Jankyneering/rack-ui/firmware/src/User/animations.c

/**
 ******************************************************************************
 * @file    animations.c
 * @brief   LED animation engine for the Charlieplex LEDs.
 *
 * The active animation is selected through register 0x0E (REG_ANIMATION):
 *   0x00 = IDLE     : custom control over the LEDs via registers 0x10-0x1B
 *   0x01 = LOADING  : rotating loading animation
 *   0x02 = FLASHING : all LEDs flash on and off
 * Register 0x0F (REG_ANIMATION_SETTINGS) holds the setting of the
 *   selected animation (timing, brightness or gauge maximum); writing
 *   REG_ANIMATION loads that animation's default.
 ******************************************************************************
 */

#include "animations.h"
#include "main.h"
#include <stdlib.h>

/* External variables from main.c */
extern volatile uint32_t sys_tick_ms;
extern volatile uint8_t device_memory[REG_COUNT];

typedef void (*Animation_Start_Fn_t)(void);
typedef void (*Animation_Step_Fn_t)(void);

/* One entry per animation exposed through register 0x0E. To add a new
 * animation: give it an ID in Animation_Id_t, implement its start/step
 * functions and append an entry here. */
typedef struct {
    uint8_t id;
    Animation_Start_Fn_t start;
    Animation_Step_Fn_t step;
} Animation_Entry_t;

/* Timing setting (register 0x0F) of the active animation and its scale, in ms
 * per register step. A scale of 0 means the register is ignored. */
static uint8_t animation_settings    = 0;
static uint8_t animation_settings_ms = 0;

static const Animation_Entry_t *Animation_Find(uint8_t id);
static void Animation_Idle_Start(void);
static void Animation_Idle_Step(void);
static void Animation_Loading_Start(void);
static void Animation_Loading_Step(void);
static void Animation_Flashing_Start(void);
static void Animation_Flashing_Step(void);
static void Animation_Pulsing_Start(void);
static void Animation_Pulsing_Step(void);
static void Animation_Breathing_Start(void);
static void Animation_Breathing_Step(void);

static void Animation_Following_Start(void);
static void Animation_Following_Step(void);
static void Animation_Point_Start(void);
static void Animation_Point_Step(void);
static void Animation_Gauge_Start(void);
static void Animation_Gauge_Step(void);
static void Animation_Gauge_Center_Start(void);
static void Animation_Gauge_Center_Step(void);

static void Animation_All_On_Start(void);
static void Animation_All_On_Step(void);
static void Animation_All_Off_Start(void);
static void Animation_All_Off_Step(void);

static const Animation_Entry_t animation_table[] = {
    {ANIMATION_IDLE, Animation_Idle_Start, Animation_Idle_Step},
    {ANIMATION_LOADING, Animation_Loading_Start, Animation_Loading_Step},
    {ANIMATION_FLASHING, Animation_Flashing_Start, Animation_Flashing_Step},
    {ANIMATION_PULSING, Animation_Pulsing_Start, Animation_Pulsing_Step},
    {ANIMATION_BREATHING, Animation_Breathing_Start, Animation_Breathing_Step},

    {ANIMATION_FOLLOWING, Animation_Following_Start, Animation_Following_Step},
    {ANIMATION_POINT, Animation_Point_Start, Animation_Point_Step},
    {ANIMATION_GAUGE, Animation_Gauge_Start, Animation_Gauge_Step},
    {ANIMATION_GAUGE_CENTER, Animation_Gauge_Center_Start, Animation_Gauge_Center_Step},

    {ANIMATION_ALL_ON, Animation_All_On_Start, Animation_All_On_Step},
    {ANIMATION_ALL_OFF, Animation_All_Off_Start, Animation_All_Off_Step},
};

static const Animation_Entry_t *active_animation = &animation_table[0];
static uint8_t current_id                        = ANIMATION_IDLE;

/* Default timing setting (register 0x0F) for a given animation id: the value
 * written to REG_ANIMATION_SETTINGS when the animation is selected. */
static uint8_t Animation_SettingsDefault(uint8_t id) {
    switch (id) {
    case ANIMATION_LOADING:
        return ANIMATION_LOADING_SETTINGS_DEFAULT;
    case ANIMATION_FLASHING:
        return ANIMATION_FLASHING_SETTINGS_DEFAULT;
    case ANIMATION_PULSING:
        return ANIMATION_PULSING_SETTINGS_DEFAULT;
    case ANIMATION_ALL_ON:
        return ANIMATION_ALL_ON_SETTINGS_DEFAULT;
    case ANIMATION_FOLLOWING:
        return ANIMATION_FOLLOWING_SETTINGS_DEFAULT;
    case ANIMATION_POINT:
        return ANIMATION_POINT_SETTINGS_DEFAULT;
    case ANIMATION_GAUGE:
        return ANIMATION_GAUGE_SETTINGS_DEFAULT;
    case ANIMATION_GAUGE_CENTER:
        return ANIMATION_GAUGE_CENTER_SETTINGS_DEFAULT;
    default:
        return 0;
    }
}

static uint8_t Animation_SettingsMs(uint8_t id) {
    switch (id) {
    case ANIMATION_LOADING:
        return ANIMATION_LOADING_SETTINGS_MS;
    case ANIMATION_FLASHING:
        return ANIMATION_FLASHING_SETTINGS_MS;
    case ANIMATION_PULSING:
        return ANIMATION_PULSING_SETTINGS_MS;
    default:
        return 0;
    }
}

static uint32_t Animation_SettingsTickMs(void) {
    return (uint32_t)animation_settings * animation_settings_ms;
}

void Animations_Init(void) {
    current_id                            = ANIMATION_DEFAULT;
    active_animation                      = Animation_Find(ANIMATION_DEFAULT);
    animation_settings                    = Animation_SettingsDefault(current_id);
    animation_settings_ms                 = Animation_SettingsMs(current_id);
    device_memory[REG_ANIMATION_SETTINGS] = animation_settings;
    active_animation->start();
}

void Animations_Set(uint8_t id) {
    const Animation_Entry_t *entry = Animation_Find(id);
    current_id                     = id;
    if (entry == NULL)
        entry = Animation_Find(ANIMATION_IDLE); // unknown value: fall back to IDLE
    if (entry != active_animation) {
        active_animation = entry;
        entry->start();
    }
    animation_settings                    = Animation_SettingsDefault(id);
    animation_settings_ms                 = Animation_SettingsMs(id);
    device_memory[REG_ANIMATION_SETTINGS] = animation_settings;
}

void Animations_SetSettings(uint8_t settings) {
    if (settings == 0) {
        // 0 keeps the current setting; undo the ISR's register write
        device_memory[REG_ANIMATION_SETTINGS] = animation_settings;
        return;
    }
    animation_settings                    = settings;
    device_memory[REG_ANIMATION_SETTINGS] = animation_settings;
    if (current_id == ANIMATION_ALL_ON) {
        for (uint8_t i = 0; i < ANIMATION_LED_COUNT; i++) {
            device_memory[REG_LED_BASE + i] = animation_settings;
        }
        APP_MarkRegsDirty();
    }
}

uint8_t Animations_GetSettings(void) {
    return animation_settings;
}

uint8_t Animations_Get(void) {
    return current_id;
}

void Animations_Tick(void) {
    static uint32_t last_tick = 0;

    if ((sys_tick_ms - last_tick) < ANIMATION_TICK_MS)
        return;
    last_tick = sys_tick_ms;

    active_animation->step();
}

static const Animation_Entry_t *Animation_Find(uint8_t id) {
    for (uint8_t i = 0; i < (sizeof(animation_table) / sizeof(animation_table[0])); i++) {
        if (animation_table[i].id == id)
            return &animation_table[i];
    }
    return NULL;
}

/**
 * @brief IDLE: the LEDs are driven manually through registers 0x10-0x1B.
 */
static void Animation_Idle_Start(void) {
    /* Nothing to reset: the master owns the LED brightness registers. */
}

static void Animation_Idle_Step(void) {
    /* Nothing to do: LED register writes are applied by the main loop. */
}

/* Standalone animations */

/**
 * @brief Perform a rotating loading animation on the Charlieplex LEDs.
 * This animation lights up each LED in a circular pattern, with each LED
 * reaching maximum brightness before moving to the next.
 */
static uint8_t loading_brightness_lut[ANIMATION_LED_COUNT];
static uint8_t loading_current_led = 0;
static uint32_t last_loading_tick  = 0;

static void Animation_Loading_Start(void) {
    // Build a simple linear LUT for the loading animation brightnesses
    for (uint8_t i = 1; i < ANIMATION_LED_COUNT; i++) {
        // Calculate the brightness for each LED in the loading animation
        loading_brightness_lut[i] =
            (uint8_t)(((uint16_t)(i + 1) * CHARLIE_PWM_STEPS) / ANIMATION_LED_COUNT - 1);
    }
    loading_current_led = 0;
    last_loading_tick   = sys_tick_ms;
}

static void Animation_Loading_Step(void) {
    uint32_t tick_ms = Animation_SettingsTickMs();
    if (tick_ms > 0 && (sys_tick_ms - last_loading_tick) >= tick_ms) {
        last_loading_tick   = sys_tick_ms;

        loading_current_led = (loading_current_led + 1) % ANIMATION_LED_COUNT;

        // Apply the calculated brightnesses to all LEDs
        for (uint8_t i = 0; i < ANIMATION_LED_COUNT; i++) {
            uint8_t led_index                       = (loading_current_led + i) % ANIMATION_LED_COUNT;
            device_memory[REG_LED_BASE + led_index] = loading_brightness_lut[i];
        }

        // Mark the registers as dirty so that the main loop applies the changes
        APP_MarkRegsDirty();
    }
}

/**
 * @brief Perform a flashing animation on the Charlieplex LEDs.
 * This animation makes all LEDs flash on and off in a synchronized manner.
 */
static uint32_t last_flashing_tick = 0;
static bool flashing_state         = false;

static void Animation_Flashing_Start(void) {
    flashing_state     = 0;
    last_flashing_tick = sys_tick_ms;
}

static void Animation_Flashing_Step(void) {
    uint32_t tick_ms = Animation_SettingsTickMs();
    if (tick_ms > 0 && (sys_tick_ms - last_flashing_tick) >= tick_ms) {
        last_flashing_tick = sys_tick_ms;

        flashing_state     = !flashing_state;

        // Apply the flashing state to all LEDs
        for (uint8_t i = 0; i < ANIMATION_LED_COUNT; i++) {
            device_memory[REG_LED_BASE + i] = flashing_state ? CHARLIE_PWM_STEPS - 1 : 0;
        }

        // Mark the registers as dirty so that the main loop applies the changes
        APP_MarkRegsDirty();
    }
}

/**
 * @brief Perform a pulsing animation on the Charlieplex LEDs.
 * This animation smoothly increases and decreases the brightness of all LEDs.
 */
static uint32_t last_pulsing_tick = 0;
static uint8_t pulsing_brightness = 0;
static int8_t pulsing_direction   = 1;

static void Animation_Pulsing_Start(void) {
    pulsing_brightness = 0;
    pulsing_direction  = 1;
    last_pulsing_tick  = sys_tick_ms;
}

static void Animation_Pulsing_Step(void) {
    uint32_t tick_ms = Animation_SettingsTickMs();
    if (tick_ms > 0 && (sys_tick_ms - last_pulsing_tick) >= tick_ms) {
        last_pulsing_tick = sys_tick_ms;

        // Update the brightness
        pulsing_brightness += pulsing_direction;

        // Change direction if we reach the limits
        if (pulsing_brightness >= CHARLIE_PWM_STEPS - 1) {
            pulsing_brightness = CHARLIE_PWM_STEPS - 1;
            pulsing_direction  = -1;
        } else if (pulsing_brightness <= 0) {
            pulsing_brightness = 0;
            pulsing_direction  = 1;
        }

        // Apply the current brightness to all LEDs
        for (uint8_t i = 0; i < ANIMATION_LED_COUNT; i++) {
            device_memory[REG_LED_BASE + i] = pulsing_brightness;
        }

        // Mark the registers as dirty so that the main loop applies the changes
        APP_MarkRegsDirty();
    }
}

/**
 * @brief Perform a breathing animation on the Charlieplex LEDs.
 * This animation smoothly increases and decreases the brightness of all LEDs.
 */
typedef enum {
    ANIMATION_BREATHING_PHASE_IN,
    ANIMATION_BREATHING_PHASE_HOLD,
    ANIMATION_BREATHING_PHASE_OUT,
    ANIMATION_BREATHING_PHASE_PAUSE,
} BreathingPhase_t;

static BreathingPhase_t breathing_phase    = ANIMATION_BREATHING_PHASE_IN;
static uint32_t breathing_phase_start_tick = 0;

static void Animation_Breathing_Start(void) {
    breathing_phase            = ANIMATION_BREATHING_PHASE_IN;
    breathing_phase_start_tick = sys_tick_ms;
}

static void Animation_Breathing_Step(void) {
    uint32_t elapsed = sys_tick_ms - breathing_phase_start_tick;

    switch (breathing_phase) {
    case ANIMATION_BREATHING_PHASE_IN:
        if (elapsed >= ANIMATION_BREATHING_IN_MS) {
            breathing_phase            = ANIMATION_BREATHING_PHASE_HOLD;
            breathing_phase_start_tick = sys_tick_ms;
            elapsed                    = 0;
        }
        break;
    case ANIMATION_BREATHING_PHASE_HOLD:
        if (elapsed >= ANIMATION_BREATHING_HOLD_MS) {
            breathing_phase            = ANIMATION_BREATHING_PHASE_OUT;
            breathing_phase_start_tick = sys_tick_ms;
            elapsed                    = 0;
        }
        break;
    case ANIMATION_BREATHING_PHASE_OUT:
        if (elapsed >= ANIMATION_BREATHING_OUT_MS) {
            breathing_phase            = ANIMATION_BREATHING_PHASE_PAUSE;
            breathing_phase_start_tick = sys_tick_ms;
            elapsed                    = 0;
        }
        break;
    case ANIMATION_BREATHING_PHASE_PAUSE:
        if (elapsed >= ANIMATION_BREATHING_PAUSE_MS) {
            breathing_phase            = ANIMATION_BREATHING_PHASE_IN;
            breathing_phase_start_tick = sys_tick_ms;
            elapsed                    = 0;
        }
        break;
    default:
        // Unknown phase, reset to IN
        breathing_phase            = ANIMATION_BREATHING_PHASE_IN;
        breathing_phase_start_tick = sys_tick_ms;
        elapsed                    = 0;
        break;
    }

    // Calculate brightness based on the current phase and elapsed time
    uint8_t brightness = 0;

    switch (breathing_phase) {
    case ANIMATION_BREATHING_PHASE_IN:
        brightness = (uint8_t)((elapsed * CHARLIE_PWM_STEPS) / ANIMATION_BREATHING_IN_MS);
        break;
    case ANIMATION_BREATHING_PHASE_HOLD:
        brightness = CHARLIE_PWM_STEPS; // Full brightness
        break;
    case ANIMATION_BREATHING_PHASE_OUT:
        brightness =
            (uint8_t)(CHARLIE_PWM_STEPS -
                      ((elapsed * CHARLIE_PWM_STEPS) / ANIMATION_BREATHING_OUT_MS));
        break;
    case ANIMATION_BREATHING_PHASE_PAUSE:
        brightness = 0; // Off
        break;
    default:
        brightness = 0; // Default to off
        break;
    }

    // Apply the calculated brightness to all LEDs
    for (uint8_t i = 0; i < ANIMATION_LED_COUNT; i++) {
        device_memory[REG_LED_BASE + i] = brightness;
    }

    // Mark the registers as dirty so that the main loop applies the changes
    APP_MarkRegsDirty();
}

/* Animations with encoder reactions */

/**
 * @brief Perform a following animation on the Charlieplex LEDs.
 * This animation lights up one in three LEDs based on the encoder rotation, creating a "following" effect.
 */
static void Animation_Following_Start(void) {
    // Nothing to reset: the master owns the LED brightness registers.
}

static void Animation_Following_Step(void) {
    // Get the current encoder rotation count
    int16_t rotation_count = (device_memory[REG_ENC_COUNT_LO] | (device_memory[REG_ENC_COUNT_HI] << 8));
    // Set LED states; the animation setting (register 0x0F) is the brightness
    // of the LEDs that are not lit
    for (uint8_t i = 0; i < ANIMATION_LED_COUNT; i++) {
        device_memory[REG_LED_BASE + i] = (i - rotation_count) % ANIMATION_FOLLOWING_LED_STEPS == 0 ? CHARLIE_PWM_STEPS - 1 : animation_settings; // Light up every third LED
    }
    // Mark the registers as dirty so that the main loop applies the changes
    APP_MarkRegsDirty();
}

/**
 * @brief Perform a point animation on the Charlieplex LEDs.
 * This animation lights up one LED at a time based on the encoder rotation, creating a "pointing" effect.
 */
static void Animation_Point_Start(void) {
    // Nothing to reset: the master owns the LED brightness registers.
}

static void Animation_Point_Step(void) {
    // Get the current encoder rotation count
    int16_t rotation_count = (device_memory[REG_ENC_COUNT_LO] | (device_memory[REG_ENC_COUNT_HI] << 8));
    // Set LED states; the animation setting (register 0x0F) is the brightness
    // of the LEDs that are not lit
    for (uint8_t i = 0; i < ANIMATION_LED_COUNT; i++) {
        device_memory[REG_LED_BASE + i] = (i - rotation_count) % CHARLIE_LED_COUNT == 0 ? CHARLIE_PWM_STEPS - 1 : animation_settings;
    }
    // Mark the registers as dirty so that the main loop applies the changes
    APP_MarkRegsDirty();
}

/**
 * @brief Perform a gauge animation on the Charlieplex LEDs.
 * This animation lights up LEDs in a gauge pattern based on the encoder rotation.
 */
static uint32_t last_gauge_tick = 0;
static void Animation_Gauge_Start(void) {
    // Reset encoder count to zero for a fresh start (signed 16-bit value)
    device_memory[REG_ENC_COUNT_HI] = 0x00;
    device_memory[REG_ENC_COUNT_LO] = 0x00;

    last_gauge_tick                 = sys_tick_ms;
}

static void Animation_Gauge_Step(void) {
    if ((sys_tick_ms - last_gauge_tick) < 50) // Update every 50ms
        return;
    last_gauge_tick = sys_tick_ms;

    // The animation setting (register 0x0F) is the maximum gauge value the
    // encoder count is scaled against (e.g. 10, 100, 250)
    int16_t gauge_max = animation_settings;

    // Get the current encoder rotation count
    int16_t rotation_count = (device_memory[REG_ENC_COUNT_LO] | (device_memory[REG_ENC_COUNT_HI] << 8));

    // Clamp the count to the 0-gauge_max range
    if (rotation_count < 0) {
        rotation_count = 0;
        // clamp device_memory[REG_ENC_COUNT_HI] and device_memory[REG_ENC_COUNT_LO] to 0
        device_memory[REG_ENC_COUNT_HI] = (uint8_t)((rotation_count >> 8) & 0xFF);
        device_memory[REG_ENC_COUNT_LO] = (uint8_t)(rotation_count & 0xFF);
    } else if (rotation_count > gauge_max) {
        rotation_count = gauge_max;
        // clamp device_memory[REG_ENC_COUNT_HI] and device_memory[REG_ENC_COUNT_LO] to gauge_max
        device_memory[REG_ENC_COUNT_HI] = (uint8_t)((rotation_count >> 8) & 0xFF);
        device_memory[REG_ENC_COUNT_LO] = (uint8_t)(rotation_count & 0xFF);
    }

#ifdef ANIMATION_GAUGE_DIM_UNUSED_LEDS
    // Hold the LEDs that are not part of the gauge arc at a low brightness
    // instead of keeping the state the previous animation left them in
    for (uint8_t i = ANIMATION_GAUGE_LED_COUNT; i < CHARLIE_LED_COUNT; i++) {
        device_memory[REG_LED_BASE + (i + ANIMATION_GAUGE_START_LED) % CHARLIE_LED_COUNT] =
            ANIMATION_GAUGE_UNUSED_BRIGHTNESS;
    }
#endif

    // calculate the brightness for each LED based on the scaled gauge value
    // the gauge is divided evenly across the arc LEDs, e.g. with a max of 100
    // and 9 LEDs, each LED covers an 11.1-unit range of the gauge
    for (uint8_t i = 0; i < ANIMATION_GAUGE_LED_COUNT; i++) {
        // calculate the value range for this LED
        float led_percentage_start = ((float)i * gauge_max) / ANIMATION_GAUGE_LED_COUNT;
        float led_percentage_end   = ((float)(i + 1) * gauge_max) / ANIMATION_GAUGE_LED_COUNT;

        if (rotation_count >= led_percentage_end) {
            // LED is fully lit
            device_memory[REG_LED_BASE + (i + ANIMATION_GAUGE_START_LED) % CHARLIE_LED_COUNT] = CHARLIE_PWM_STEPS - 1;
        } else if (rotation_count <= led_percentage_start) {
            // LED is off
            device_memory[REG_LED_BASE + (i + ANIMATION_GAUGE_START_LED) % CHARLIE_LED_COUNT] = 0;
        } else {
            // LED is partially lit, calculate brightness based on the scaled value
            float led_range                                                                   = led_percentage_end - led_percentage_start;
            float led_brightness_percentage                                                   = (rotation_count - led_percentage_start) / led_range;
            device_memory[REG_LED_BASE + (i + ANIMATION_GAUGE_START_LED) % CHARLIE_LED_COUNT] = (uint8_t)(led_brightness_percentage * (CHARLIE_PWM_STEPS - 1));
        }
    }

    // Mark the registers as dirty so that the main loop applies the changes
    APP_MarkRegsDirty();
}

/**
 * @brief Perform a centered gauge animation on the Charlieplex LEDs.
 * This animation lights up LEDs outward from the center LED based on the
 * encoder rotation: positive counts fill one direction, negative counts the
 * other, up to the positive/negative limit set through register 0x0F.
 */
static uint32_t last_gauge_center_tick = 0;
static void Animation_Gauge_Center_Start(void) {
    // Reset encoder count to zero for a fresh start (signed 16-bit value)
    device_memory[REG_ENC_COUNT_HI] = 0x00;
    device_memory[REG_ENC_COUNT_LO] = 0x00;

    last_gauge_center_tick          = sys_tick_ms;
}

static void Animation_Gauge_Center_Step(void) {
    if ((sys_tick_ms - last_gauge_center_tick) < 50) // Update every 50ms
        return;
    last_gauge_center_tick = sys_tick_ms;

    // The animation setting (register 0x0F) is the positive/negative gauge
    // limit the encoder count is scaled against (e.g. 10, 100, 250); the count
    // is clamped symmetrically to -gauge_center_max..+gauge_center_max
    int16_t gauge_center_max = animation_settings;

    // Get the current encoder rotation count
    int16_t rotation_count = (device_memory[REG_ENC_COUNT_LO] | (device_memory[REG_ENC_COUNT_HI] << 8));

    // Clamp the count to the -gauge_center_max..+gauge_center_max range
    if (rotation_count < -(gauge_center_max)) {
        rotation_count = -(gauge_center_max);
        // clamp device_memory[REG_ENC_COUNT_HI] and device_memory[REG_ENC_COUNT_LO] to -(gauge_center_max)
        device_memory[REG_ENC_COUNT_HI] = (uint8_t)((rotation_count >> 8) & 0xFF);
        device_memory[REG_ENC_COUNT_LO] = (uint8_t)(rotation_count & 0xFF);
    } else if (rotation_count > gauge_center_max) {
        rotation_count = gauge_center_max;
        // clamp device_memory[REG_ENC_COUNT_HI] and device_memory[REG_ENC_COUNT_LO] to gauge_max
        device_memory[REG_ENC_COUNT_HI] = (uint8_t)((rotation_count >> 8) & 0xFF);
        device_memory[REG_ENC_COUNT_LO] = (uint8_t)(rotation_count & 0xFF);
    }

#ifdef ANIMATION_GAUGE_DIM_UNUSED_LEDS
    // Hold the LEDs that are not part of the gauge arc at a low brightness
    // instead of keeping the state the previous animation left them in
    for (uint8_t i = ANIMATION_GAUGE_LED_COUNT; i < CHARLIE_LED_COUNT; i++) {
        device_memory[REG_LED_BASE + (i + ANIMATION_GAUGE_START_LED) % CHARLIE_LED_COUNT] =
            ANIMATION_GAUGE_UNUSED_BRIGHTNESS;
    }
#endif

    // calculate the brightness for each LED based on the scaled gauge value
    // the gauge is divided evenly across the arc LEDs going up or down from the
    // center LED, e.g. with a min/max of 50 and 4 LEDs per side, each LED covers
    // a 12.5-unit range of the gauge. The center LED is always lit at full
    // brightness, the LEDs to the left and right of it are lit based on the
    // encoder count, up to the 4th LED on either side of the center LED.
    int value                 = abs((int)rotation_count);
    bool is_negative          = rotation_count < 0;
    uint8_t side_led_count    = (ANIMATION_GAUGE_LED_COUNT - 1) / 2;
    uint8_t center_led        = (ANIMATION_GAUGE_START_LED + side_led_count) % CHARLIE_LED_COUNT;

    // Center LED is always lit at full brightness
    device_memory[REG_LED_BASE + center_led] = CHARLIE_PWM_STEPS - 1;

    for (uint8_t i = 0; i < side_led_count; i++) {
        // calculate the value range for this LED
        float led_percentage_start = ((float)i * gauge_center_max) / side_led_count;
        float led_percentage_end   = ((float)(i + 1) * gauge_center_max) / side_led_count;

        uint8_t level = 0;
        if (value >= led_percentage_end) {
            // LED is fully lit
            level = CHARLIE_PWM_STEPS - 1;
        } else if (value <= led_percentage_start) {
            // LED is off
            level = 0;
        } else {
            // LED is partially lit, calculate brightness based on the scaled value
            float led_range                  = led_percentage_end - led_percentage_start;
            float led_brightness_percentage  = (value - led_percentage_start) / led_range;
            level                            = (uint8_t)(led_brightness_percentage * (CHARLIE_PWM_STEPS - 1));
        }

        // write both sides every step so the inactive side is turned off
        // instead of keeping the level it had before the count flipped sign
        int8_t offset = (int8_t)(i + 1);
        uint8_t positive_led = (uint8_t)(center_led + CHARLIE_LED_COUNT + offset) % CHARLIE_LED_COUNT;
        uint8_t negative_led = (uint8_t)(center_led + CHARLIE_LED_COUNT - offset) % CHARLIE_LED_COUNT;
        device_memory[REG_LED_BASE + positive_led] = is_negative ? 0 : level;
        device_memory[REG_LED_BASE + negative_led] = is_negative ? level : 0;
    }

    // Mark the registers as dirty so that the main loop applies the changes
    APP_MarkRegsDirty();
}

/**
 * @brief Turn all LEDs on at set brightness.
 * The brightness is the animation setting (register 0x0F).
 */
static void Animation_All_On_Start(void) {
    // No startup action needed; the step function will set the brightness.
}
static void Animation_All_On_Step(void) {
    for (uint8_t i = 0; i < ANIMATION_LED_COUNT; i++) {
        device_memory[REG_LED_BASE + i] = animation_settings;
    }

    // Mark the registers as dirty so that the main loop applies the changes
    APP_MarkRegsDirty();
}

/**
 * @brief Turn all LEDs off.
 */
static void Animation_All_Off_Start(void) {
    // No startup action needed; the step function will turn off the LEDs.
}
static void Animation_All_Off_Step(void) {
    for (uint8_t i = 0; i < ANIMATION_LED_COUNT; i++) {
        device_memory[REG_LED_BASE + i] = 0;
    }
    APP_MarkRegsDirty();
}
