Jankyneering/rack-ui/software/scripts/ssd1306.py

"""Minimal SSD1306 128x64 OLED driver for the host-side test scripts.

Drives the display directly through an i2cdriver.I2CDriver instance on the
same bus as the rack-ui MCU, so no firmware changes are needed. No external
dependencies: a classic 5x7 bitmap font is embedded.

Coordinate system: (0,0) is the top-left corner, x grows to the right, y grows
down. The framebuffer is page-major: one byte per column covers 8 vertical
pixels, LSB = topmost row of the page. On the common two-color modules the
top 16 rows (y 0-15) are yellow and the rest is blue, which makes rows 0-15 a
natural title band.

The SSD1306 GDDRAM is undefined at power-up, so init() pushes a full clear to
the display. Only dirty pages are re-sent afterwards; the shadow copy of the
last flushed content makes that bookkeeping possible.
"""

WIDTH = 128
HEIGHT = 64
PAGE_COUNT = HEIGHT // 8

I2C_ADDRESSES = (0x3C, 0x3D)

# Control bytes: Co=0 (following bytes all share this D/C state)
CMD = 0x00
DATA = 0x40

# Classic 5x7 bitmap font, ASCII 0x20-0x7E, 5 bytes per glyph, LSB = top row.
FONT5X7 = (
    0x00, 0x00, 0x00, 0x00, 0x00, 0x00, 0x00, 0x5F, 0x00, 0x00, 0x00, 0x07,
    0x00, 0x07, 0x00, 0x14, 0x7F, 0x14, 0x7F, 0x14, 0x24, 0x2A, 0x7F, 0x2A,
    0x12, 0x23, 0x13, 0x08, 0x64, 0x62, 0x36, 0x49, 0x56, 0x20, 0x50, 0x00,
    0x08, 0x07, 0x03, 0x00, 0x00, 0x1C, 0x22, 0x41, 0x00, 0x00, 0x41, 0x22,
    0x1C, 0x00, 0x2A, 0x1C, 0x7F, 0x1C, 0x2A, 0x08, 0x08, 0x3E, 0x08, 0x08,
    0x00, 0x80, 0x70, 0x30, 0x00, 0x08, 0x08, 0x08, 0x08, 0x08, 0x00, 0x00,
    0x60, 0x60, 0x00, 0x20, 0x10, 0x08, 0x04, 0x02, 0x3E, 0x51, 0x49, 0x45,
    0x3E, 0x00, 0x42, 0x7F, 0x40, 0x00, 0x72, 0x49, 0x49, 0x49, 0x46, 0x21,
    0x41, 0x49, 0x4D, 0x33, 0x18, 0x14, 0x12, 0x7F, 0x10, 0x27, 0x45, 0x45,
    0x45, 0x39, 0x3C, 0x4A, 0x49, 0x49, 0x31, 0x41, 0x21, 0x11, 0x09, 0x07,
    0x36, 0x49, 0x49, 0x49, 0x36, 0x46, 0x49, 0x49, 0x29, 0x1E, 0x00, 0x00,
    0x14, 0x00, 0x00, 0x00, 0x40, 0x34, 0x00, 0x00, 0x00, 0x08, 0x14, 0x22,
    0x41, 0x14, 0x14, 0x14, 0x14, 0x14, 0x00, 0x41, 0x22, 0x14, 0x08, 0x02,
    0x01, 0x59, 0x09, 0x06, 0x3E, 0x41, 0x5D, 0x59, 0x4E, 0x7C, 0x12, 0x11,
    0x12, 0x7C, 0x7F, 0x49, 0x49, 0x49, 0x36, 0x3E, 0x41, 0x41, 0x41, 0x22,
    0x7F, 0x41, 0x41, 0x41, 0x3E, 0x7F, 0x49, 0x49, 0x49, 0x41, 0x7F, 0x09,
    0x09, 0x09, 0x01, 0x3E, 0x41, 0x41, 0x51, 0x73, 0x7F, 0x08, 0x08, 0x08,
    0x7F, 0x00, 0x41, 0x7F, 0x41, 0x00, 0x20, 0x40, 0x41, 0x3F, 0x01, 0x7F,
    0x08, 0x14, 0x22, 0x41, 0x7F, 0x40, 0x40, 0x40, 0x40, 0x7F, 0x02, 0x1C,
    0x02, 0x7F, 0x7F, 0x04, 0x08, 0x10, 0x7F, 0x3E, 0x41, 0x41, 0x41, 0x3E,
    0x7F, 0x09, 0x09, 0x09, 0x06, 0x3E, 0x41, 0x51, 0x21, 0x5E, 0x7F, 0x09,
    0x19, 0x29, 0x46, 0x26, 0x49, 0x49, 0x49, 0x32, 0x03, 0x01, 0x7F, 0x01,
    0x03, 0x3F, 0x40, 0x40, 0x40, 0x3F, 0x1F, 0x20, 0x40, 0x20, 0x1F, 0x3F,
    0x40, 0x38, 0x40, 0x3F, 0x63, 0x14, 0x08, 0x14, 0x63, 0x03, 0x04, 0x78,
    0x04, 0x03, 0x61, 0x59, 0x49, 0x4D, 0x43, 0x00, 0x7F, 0x41, 0x41, 0x41,
    0x02, 0x04, 0x08, 0x10, 0x20, 0x00, 0x41, 0x41, 0x41, 0x7F, 0x04, 0x02,
    0x01, 0x02, 0x04, 0x40, 0x40, 0x40, 0x40, 0x40, 0x00, 0x03, 0x07, 0x08,
    0x00, 0x20, 0x54, 0x54, 0x78, 0x40, 0x7F, 0x28, 0x44, 0x44, 0x38, 0x38,
    0x44, 0x44, 0x44, 0x28, 0x38, 0x44, 0x44, 0x28, 0x7F, 0x38, 0x54, 0x54,
    0x54, 0x18, 0x00, 0x08, 0x7E, 0x09, 0x02, 0x18, 0xA4, 0xA4, 0x9C, 0x78,
    0x7F, 0x08, 0x04, 0x04, 0x78, 0x00, 0x44, 0x7D, 0x40, 0x00, 0x20, 0x40,
    0x40, 0x3D, 0x00, 0x7F, 0x10, 0x28, 0x44, 0x00, 0x00, 0x41, 0x7F, 0x40,
    0x00, 0x7C, 0x04, 0x78, 0x04, 0x78, 0x7C, 0x08, 0x04, 0x04, 0x78, 0x38,
    0x44, 0x44, 0x44, 0x38, 0xFC, 0x18, 0x24, 0x24, 0x18, 0x18, 0x24, 0x24,
    0x18, 0xFC, 0x7C, 0x08, 0x04, 0x04, 0x08, 0x48, 0x54, 0x54, 0x54, 0x24,
    0x04, 0x04, 0x3F, 0x44, 0x24, 0x3C, 0x40, 0x40, 0x20, 0x7C, 0x1C, 0x20,
    0x40, 0x20, 0x1C, 0x3C, 0x40, 0x30, 0x40, 0x3C, 0x44, 0x28, 0x10, 0x28,
    0x44, 0x4C, 0x90, 0x90, 0x90, 0x7C, 0x44, 0x64, 0x54, 0x4C, 0x44, 0x00,
    0x08, 0x36, 0x41, 0x00, 0x00, 0x00, 0x77, 0x00, 0x00, 0x00, 0x41, 0x36,
    0x08, 0x00, 0x02, 0x01, 0x02, 0x04, 0x02,
)

FONT_WIDTH = 5
FONT_HEIGHT = 7
FONT_ADVANCE = FONT_WIDTH + 1  # one blank column between characters


class SSD1306:
    def __init__(self, i2c, address=0x3C, width=WIDTH, height=HEIGHT):
        self.i2c = i2c
        self.address = address
        self.width = width
        self.height = height
        self.pages = height // 8
        self.buffer = bytearray(width * self.pages)
        self.shadow = bytearray(width * self.pages)
        self.init()

    def init(self):
        mux = self.height - 1
        com_pins = 0x12 if self.pages > 4 else 0x02
        self.command(
            0xAE,  # display off
            0xD5, 0x80,  # clock divide / oscillator
            0xA8, mux,  # multiplex ratio
            0xD3, 0x00,  # display offset
            0x40,  # display start line 0
            0x8D, 0x14,  # charge pump enable
            0x20, 0x00,  # horizontal addressing mode
            0xA1,  # segment remap: column 127 = SEG0
            0xC8,  # COM scan direction: remapped
            0xDA, com_pins,  # COM pins configuration
            0x81, 0x8F,  # contrast
            0xD9, 0x22,  # pre-charge period
            0xDB, 0x40,  # VCOMH deselect level
            0xA4,  # display follows RAM
            0xA6,  # normal (non-inverted) display
        )
        # GDDRAM is undefined at power-up: force a full clear before enabling the
        # panel, and sync the shadow so the first dirty-page flush is correct.
        for page in range(self.pages):
            self._set_window(page)
            self.i2c.start(self.address, 0)
            self.i2c.write(bytes([DATA]) + bytes(self.width))
            self.i2c.stop()
        self.command(0xAF)  # display on

    def command(self, *cmds):
        self.i2c.start(self.address, 0)
        self.i2c.write(bytes([CMD]) + bytes(cmds))
        self.i2c.stop()

    def power(self, on):
        self.command(0xAF if on else 0xAE)

    def invert(self, on):
        self.command(0xA7 if on else 0xA6)

    # --- framebuffer ---

    def clear(self):
        self.buffer = bytearray(len(self.buffer))

    def pixel(self, x, y, on=True):
        if not (0 <= x < self.width and 0 <= y < self.height):
            return
        page, bit = y >> 3, y & 7
        index = page * self.width + x
        if on:
            self.buffer[index] |= 1 << bit
        else:
            self.buffer[index] &= ~(1 << bit) & 0xFF

    def fill_rect(self, x, y, w, h, on=True):
        for dy in range(h):
            for dx in range(w):
                self.pixel(x + dx, y + dy, on)

    def rect(self, x, y, w, h, on=True):
        self.hline(x, y, w, on)
        self.hline(x, y + h - 1, w, on)
        self.vline(x, y, h, on)
        self.vline(x + w - 1, y, h, on)

    def hline(self, x, y, w, on=True):
        for dx in range(w):
            self.pixel(x + dx, y, on)

    def vline(self, x, y, h, on=True):
        for dy in range(h):
            self.pixel(x, y + dy, on)

    # --- text ---

    def text(self, x, y, s, on=True):
        """Draw a string with the 5x7 font; returns the x after the last glyph."""
        for ch in s:
            code = ord(ch)
            if not (0x20 <= code <= 0x7E):
                code = 0x20
            glyph = FONT5X7[(code - 0x20) * FONT_WIDTH : (code - 0x20 + 1) * FONT_WIDTH]
            for col, bits in enumerate(glyph):
                for row in range(FONT_HEIGHT):
                    if bits & (1 << row):
                        self.pixel(x + col, y + row, on)
            x += FONT_ADVANCE
        return x

    def text_width(self, s):
        return len(s) * FONT_ADVANCE - 1 if s else 0

    def text_centered(self, y, s, on=True):
        self.text(max(0, (self.width - self.text_width(s)) // 2), y, s, on)

    # --- transfer ---

    def _set_window(self, page):
        self.command(0x21, 0, self.width - 1, 0x22, page, page)

    def flush(self):
        """Send only the pages whose contents changed since the last flush."""
        for page in range(self.pages):
            start = page * self.width
            seg = self.buffer[start : start + self.width]
            if seg == self.shadow[start : start + self.width]:
                continue
            self._set_window(page)
            self.i2c.start(self.address, 0)
            self.i2c.write(bytes([DATA]) + bytes(seg))
            self.i2c.stop()
            self.shadow[start : start + self.width] = seg


def probe(i2c):
    """Return an initialized SSD1306 for the first display found on the bus,
    or None when no display answers (it is an optional board component)."""
    scan = getattr(i2c, "scan", None)
    if scan is not None:
        try:
            found = scan(silent=True)
        except TypeError:
            found = scan()
        for address in I2C_ADDRESSES:
            if address in found:
                return SSD1306(i2c, address)
        return None
    for address in I2C_ADDRESSES:
        try:
            return SSD1306(i2c, address)
        except Exception:
            continue
    return None
